JennyDigital/DCDeluxe/Core/Inc/main.h

#define AUDIO_Pin GPIO_PIN_4
#define AUDIO_GPIO_Port GPIOA
#define UNLOCK_Pin GPIO_PIN_3
#define UNLOCK_GPIO_Port GPIOB
#define TRIGGER_Pin GPIO_PIN_4
#define TRIGGER_GPIO_Port GPIOB
#define OPT4_Pin GPIO_PIN_5
#define OPT4_GPIO_Port GPIOB
#define OPT3_Pin GPIO_PIN_6
#define OPT3_GPIO_Port GPIOB
#define OPT2_Pin GPIO_PIN_7
#define OPT2_GPIO_Port GPIOB
#define OPT1_Pin GPIO_PIN_9
#define OPT1_GPIO_Port GPIOB
