JennyDigital/DCDeluxe/Core/Inc/wave.h

#ifndef _WAVETABLE_H
#define  _WAVETABLE_H

const int16_t wave[ WAVETABLE_SZ ] =
  {
         0,       1,       3,       4,       6,       7,       9,      10,
        12,      14,      15,      17,      18,      20,      21,      23,
        25,      26,      28,      29,      31,      32,      34,      36,
        37,      39,      40,      42,      43,      45,      47,      48,
        50,      51,      53,      54,      56,      58,      59,      61,
        62,      64,      65,      67,      69,      70,      72,      73,
        75,      76,      78,      80,      81,      83,      84,      86,
        87,      89,      91,      92,      94,      95,      97,      98,
       100,     102,     103,     105,     106,     108,     109,     111,
       113,     114,     116,     117,     119,     120,     122,     124,
       125,     127,     128,     130,     131,     133,     135,     136,
       138,     139,     141,     142,     144,     146,     147,     149,
       150,     152,     153,     155,     157,     158,     160,     161,
       163,     164,     166,     168,     169,     171,     172,     174,
       175,     177,     179,     180,     182,     183,     185,     186,
       188,     189,     191,     193,     194,     196,     197,     199,
       200,     202,     204,     205,     207,     208,     210,     211,
       213,     215,     216,     218,     219,     221,     222,     224,
       226,     227,     229,     230,     232,     233,     235,     237,
       238,     240,     241,     243,     244,     246,     248,     249,
       251,     252,     254,     255,     257,     259,     260,     262,
       263,     265,     266,     268,     269,     271,     273,     274,
       276,     277,     279,     280,     282,     284,     285,     287,
       288,     290,     291,     293,     295,     296,     298,     299,
       301,     302,     304,     306,     307,     309,     310,     312,
       313,     315,     316,     318,     320,     321,     323,     324,
       326,     327,     329,     331,     332,     334,     335,     337,
       338,     340,     342,     343,     345,     346,     348,     349,
       351,     352,     354,     356,     357,     359,     360,     362,
       363,     365,     367,     368,     370,     371,     373,     374,
       376,     378,     379,     381,     382,     384,     385,     387,
       388,     390,     392,     393,     395,     396,     398,     399,
       401,     403,     404,     406,     407,     409,     410,     412,
       413,     415,     417,     418,     420,     421,     423,     424,
       426,     428,     429,     431,     432,     434,     435,     437,
       438,     440,     442,     443,     445,     446,     448,     449,
       451,     453,     454,     456,     457,     459,     460,     462,
       463,     465,     467,     468,     470,     471,     473,     474,
       476,     478,     479,     481,     482,     484,     485,     487,
       488,     490,     492,     493,     495,     496,     498,     499,
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
  };

#endif // End of _WAVEFILE_H
