JennyDigital/DCDeluxe/Core/Inc/notes.h

#ifndef _NOTES_H
#define _NOTES_H

#define nC3     130.813
#define nCS3    138.591
#define nDB3    CS3
#define nD3     146.832
#define nD3S    155.563
#define nE3B    nD3S
#define nE3     164.184
#define nF3     174.614
#define nF3S    184.997
#define nG3B    nF3S
#define nG3     195.998
#define nG3S    207.652
#define nA3B    nG3S
#define nA3     220
#define nA3S    233.082
#define nB3B    nA3S

#define nC4     261.626
#define nC4S    277.183
#define nD4B    nC4S
#define nD4     293.665
#define nD4S    311.127
#define nE4B    nD4S
#define nE4     329.628
#define nF4     349.228
#define nF4S    369.994
#define nG4B    nF4S
#define nG4     391.995
#define nG4S    415.305
#define nA4B    nG4S
#define nA4     440
#define nA4S    466.164
#define nB4B    nA4S
#define nB4     493.883

#define nC5     523.251
#define nC5S    554.365
#define nD5B    nC5S
#define nD5     587.330
#define nD5S    622.254
#define nE5B    nD5S
#define nE5     659.255
#define nF5     698.456
#define nF5S    739.989
#define nG5B    nF5S
#define nG5     783.991
#define nG5S    830.609
#define nA5B    nG5S
#define nA5     880
#define nA5S    932.328
#define nB5B    nA5S
#define nB5     987.767

#define nC6     1046.50
#define nC6S    1108.73
#define nD6B    nC6S
#define nD6     1174.66
#define nD6S    1244.51
#define nE6B    nD6S
#define nE6     1318.51
#define nF6     1396.91
#define nF6S    1479.98
#define nG6B    nF6S
#define nG6     1567.98
#define nG6S    1661.22
#define nA6B    nG6S
#define nA6     1760
#define nB6     1975.53

// Special control notes
//
#define END_PLAY    0
#endif
